eokgnah/ZOE-Display/Platine V8/Bilder/Adafruit kapazitives Display neue Version.jpg

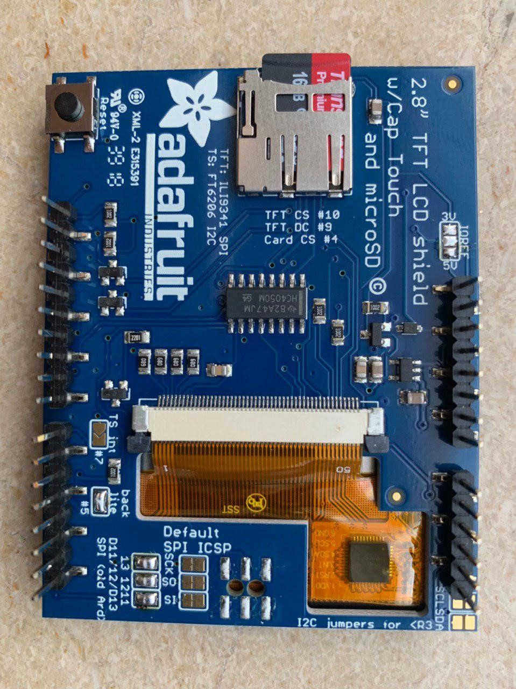
Platine V8/Bilder/Adafruit kapazitives Display neue Version.jpg
