eokgnah/ZOE-Display/Platine V8/Schaltplan Seite 1.png

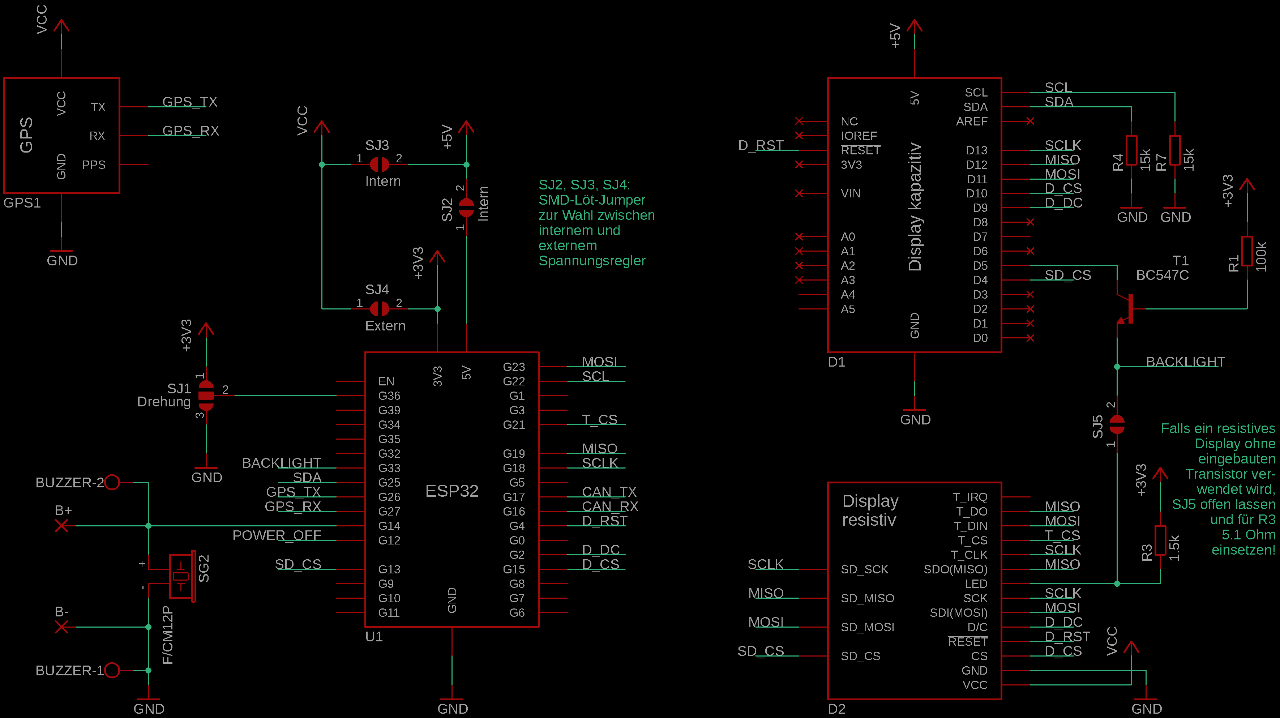
Platine V8/Schaltplan Seite 1.png
